denglerchr/Wheeled-Inverted-Pendulum/02_Software/Teensy/mpu_readout.ino

void mpu_readout()
{
  // wait for MPU interrupt or extra packet(s) available
  if (!dmpReady || (!mpuInterrupt && fifoCount < packetSize)) return;


  // reset interrupt flag and get INT_STATUS byte
  mpuInterrupt = false;
  mpuIntStatus = mpu.getIntStatus();

  // get current FIFO count
  fifoCount = mpu.getFIFOCount();

  // check for overflow (this should never happen unless our code is too inefficient)
  if ((mpuIntStatus & 0x10) || fifoCount == 1024)
  {
      // reset so we can continue cleanly
      mpu.resetFIFO();
      Serial.println(F("FIFO overflow!"));
  }

  // otherwise, check for DMP data ready interrupt (this should happen frequently)
  else if (mpuIntStatus & 0x02)
  {
      // wait for correct available data length, should be a VERY short wait
      while (fifoCount < packetSize) fifoCount = mpu.getFIFOCount();

      // read a packet from FIFO
      mpu.getFIFOBytes(fifoBuffer, packetSize);

      // track FIFO count here in case there is > 1 packet available
      // (this lets us immediately read more without waiting for an interrupt)
      fifoCount -= packetSize;

      // get ypr
      mpu.dmpGetQuaternion(&q, fifoBuffer);
      mpu.dmpGetGyro(gyr, fifoBuffer);
      mpu.dmpGetGravity(&gravity, &q);
      mpu.dmpGetYawPitchRoll(ypr, &q, &gravity);

      //reset
      mpu.resetFIFO();

  }


}
